mignon-p/A2JoystickAdapter/Joystick.sch

## KiCad design Joystick.sch (2018-09-17, an earlier design)

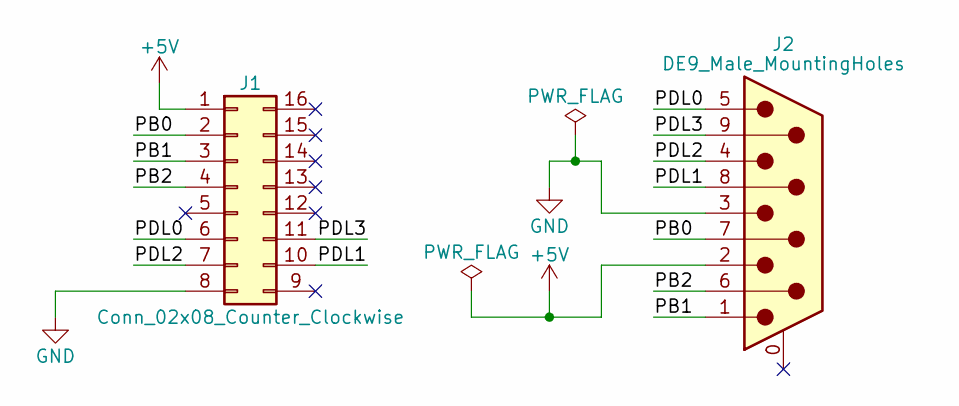
[picture p5: schematic Joystick.sch]

Parts:
J1: Conn_02x08_Counter_Clockwise; DIP-16_W7.62mm_Socket; MPN A 16-LC-TT; Digi-Key_PN AE9992-ND
J2: DE9_Male_MountingHoles; DSUB-9_Male_Horizontal_P2.77x2.84mm_EdgePinOffset7.70mm_Hou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; MPN A-DS 09 A/KG-T2S; Digi-Key_PN AE10968-ND

Connections:
+5V: J1.1, J2.2
GND: J1.8, J2.3
PB0: J1.2, J2.7
PB1: J1.3, J2.1
PB2: J1.4, J2.6
PDL0: J1.6, J2.5
PDL1: J1.10, J2.8
PDL2: J1.7, J2.4
PDL3: J1.11, J2.9
